Elecrow-RD/nRF52840/sendATcommands_new/Param_Var.c

#include "Param_Var.h"

app_param_t app_param = {
  .param_len = 0,
  .lora_info = {
    // .DevEui = 0x70B3D57ED006CFAA,
    // .JoinEui = 0x3333333344444444,
    // .DeviceKey = { 0x00, 0x00, 0x00, 0x00, 0x00, 0x00, 0x00, 0x00, 0x00, 0x00, 0x00, 0x00, 0x00, 0x00, 0x00, 0x00 },
    // .AppKey = { 0x20, 0x68, 0xBC, 0x89, 0xA6, 0x89, 0xA1, 0x64, 0xD6, 0xE1, 0x95, 0xBA, 0xFF, 0xB2, 0x83, 0x69 }, //915

    // .DevEui = 0x70B3D57ED006CFA9,
    // .JoinEui = 0x1111111122222222,
    // .DeviceKey = { 0x00, 0x00, 0x00, 0x00, 0x00, 0x00, 0x00, 0x00, 0x00, 0x00, 0x00, 0x00, 0x00, 0x00, 0x00, 0x00 },
    // .AppKey = { 0xBE, 0x4C, 0xA9, 0x72, 0xED, 0xE2, 0x4F, 0xA7, 0x84, 0x77, 0xF6, 0xFF, 0x39, 0x0D, 0xC3, 0x79 }, //868

    .JoinEui = 0x6464646464646464,
    .DevEui = 0x70B3D57ED006D427,
    .DeviceKey = { 0x00, 0x00, 0x00, 0x00, 0x00, 0x00, 0x00, 0x00, 0x00, 0x00, 0x00, 0x00, 0x00, 0x00, 0x00, 0x00 },
    .AppKey = { 0x6E, 0xDA, 0x62, 0x8C, 0xF1, 0x22, 0x83, 0xAB, 0xB9, 0x97, 0xBC, 0x20, 0x62, 0xE3, 0x0D, 0xF7 }, //868

    .ActiveRegion = 0,    // 0: EU868, 1: US915
    .ActivationType = 2,  // 0: none, 1: ABP, 2: OTAA
    .ADR = 0,             // 0: false, 1: true
    .DR = 2,              // 0 - 7    915->0 868->2
    .dutyCycleEnabled = 1,
    .msPerHour = 1250,
    .txPower = 22,
    .rx2dr = 5,
    .ChannelGroup = 1,  // 0 - 7, only for AU915 and US915
    .DevAddr = 0x00000000,
    .DeviceCode = { 0x00, 0x00, 0x00, 0x00, 0x00, 0x00, 0x00, 0x00 },
    .NwkKey = { 0x00, 0x00, 0x00, 0x00, 0x00, 0x00, 0x00, 0x00, 0x00, 0x00, 0x00, 0x00, 0x00, 0x00, 0x00, 0x00 },
    .AppSKey = { 0x00, 0x00, 0x00, 0x00, 0x00, 0x00, 0x00, 0x00, 0x00, 0x00, 0x00, 0x00, 0x00, 0x00, 0x00, 0x00 },
    .NwkSKey = { 0x00, 0x00, 0x00, 0x00, 0x00, 0x00, 0x00, 0x00, 0x00, 0x00, 0x00, 0x00, 0x00, 0x00, 0x00, 0x00 },
    .FnwksKey = { 0x00, 0x00, 0x00, 0x00, 0x00, 0x00, 0x00, 0x00, 0x00, 0x00, 0x00, 0x00, 0x00, 0x00, 0x00, 0x00 },
    .SnwksKey = { 0x00, 0x00, 0x00, 0x00, 0x00, 0x00, 0x00, 0x00, 0x00, 0x00, 0x00, 0x00, 0x00, 0x00, 0x00, 0x00 },
  },
  .crc = 0,
};

pos_msg_file_id_t pos_msg_file_id = {
  .reboot_cnt = 0,
  .log_cnt = 0,
};
pos_msg_param_t pos_msg_param = {
  0
};

gnss_group_param_t app_gnss_group_param = {
  .group_id = 0,
};


append_param_t app_append_param = {
  .Platform = IOT_PLATFORM_SENSECAP_TTN,  // 0: SENSECAP_TTN, 1: OTHER, 2: Helium, 3: TTN, 4:SENSECAP_HELIUM
  .Retry = 1,
  .cache_en = true,
  .position_interval = 5,
  .sample_interval = 5,
};

uint16_t track_gnss_group_id = 0;
